JoshWilbur/Electronic-Speed-Controller/Schematics/H_Bridge_SchematicV3.pdf

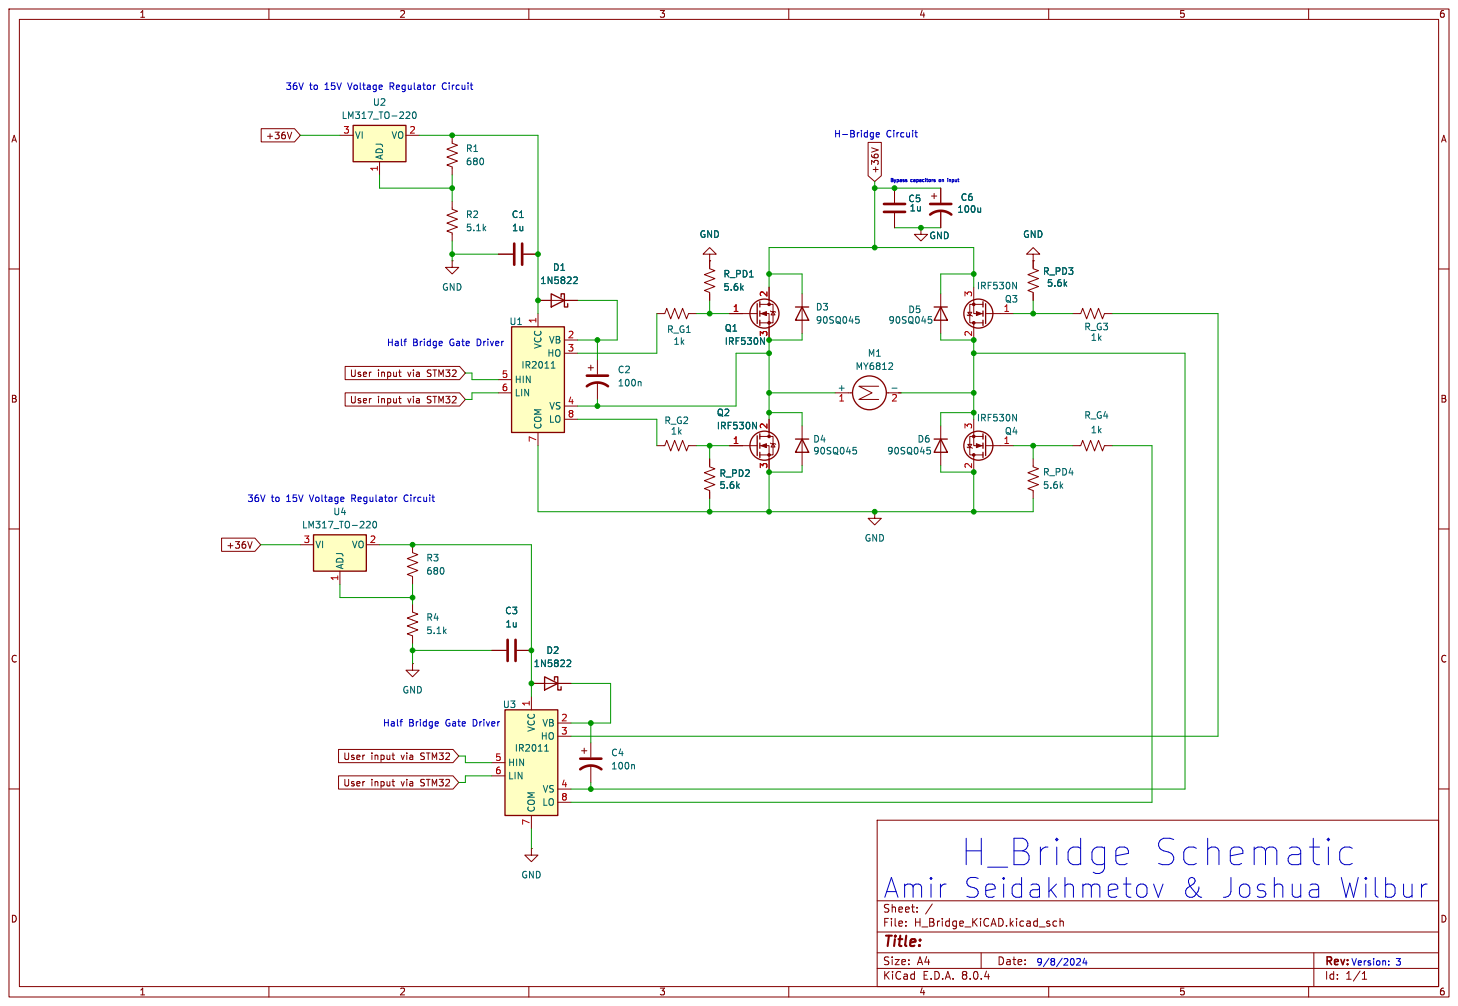
[picture p34: page 1]

Id: 1/1 Title: File: H_Bridge_KiCAD.kicad_sch Sheet: / VCC

1 VB 2 HO 3 VS 4 HIN 5

Half Bridge Gate Driver
