JoshWilbur/Electronic-Speed-Controller/Schematics/H_Bridge_SchematicV2.pdf

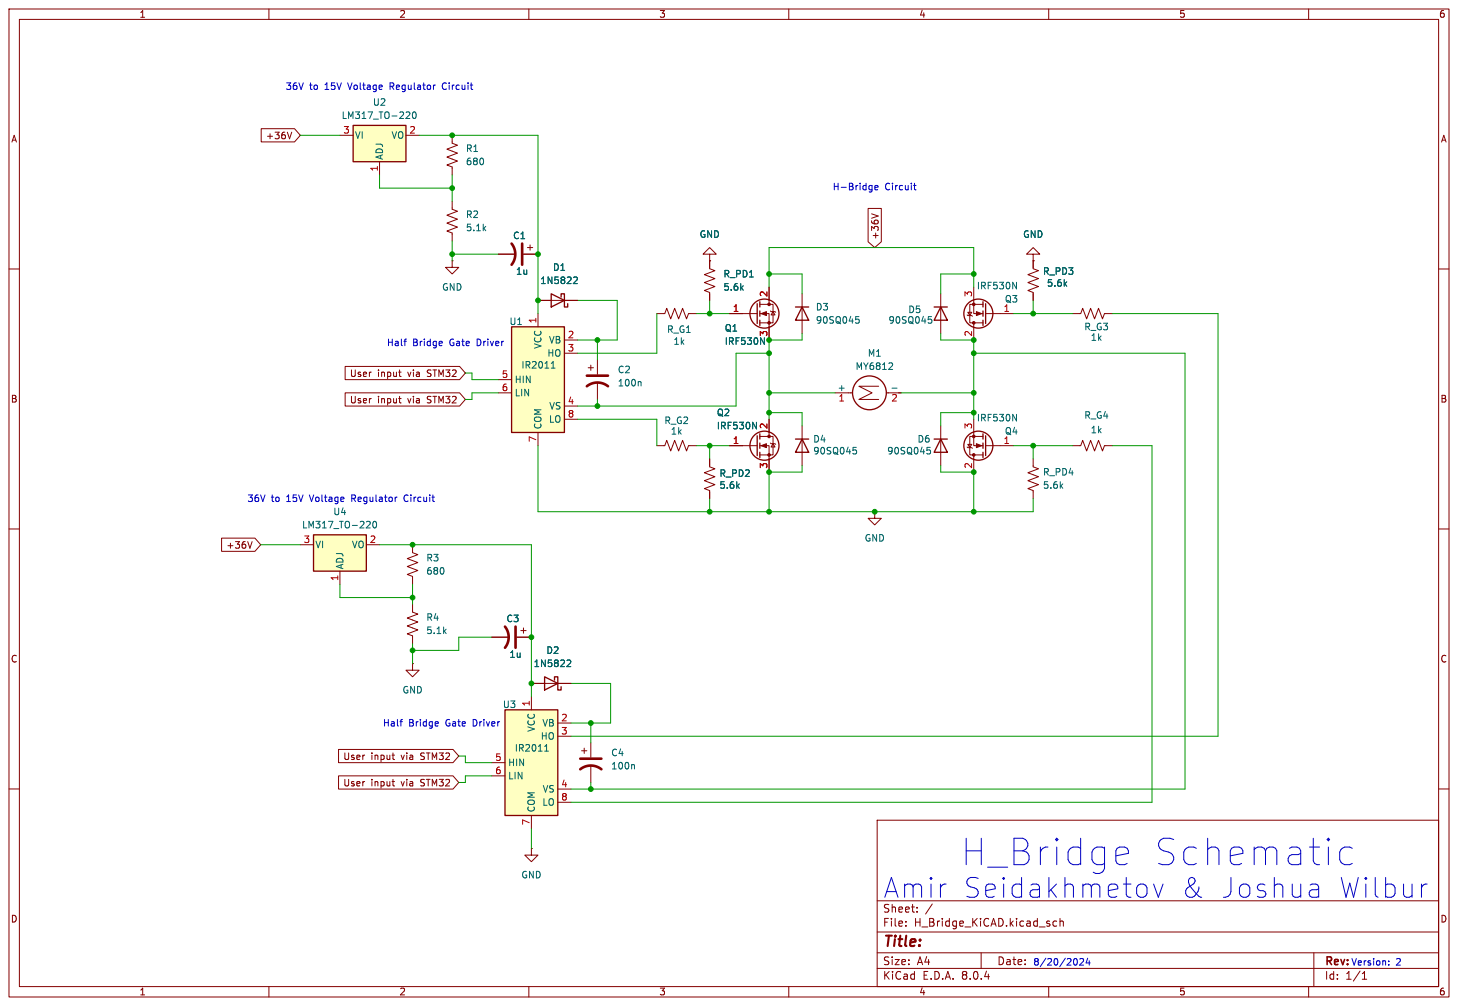
[picture p35: page 1]

1 VB 2 HO 3 VS 4 HIN 5

Id: 1/1 Title: File: H_Bridge_KiCAD.kicad_sch Sheet: /
