JoshWilbur/Electronic-Speed-Controller/Schematics/H_Bridge_SchematicV4.pdf

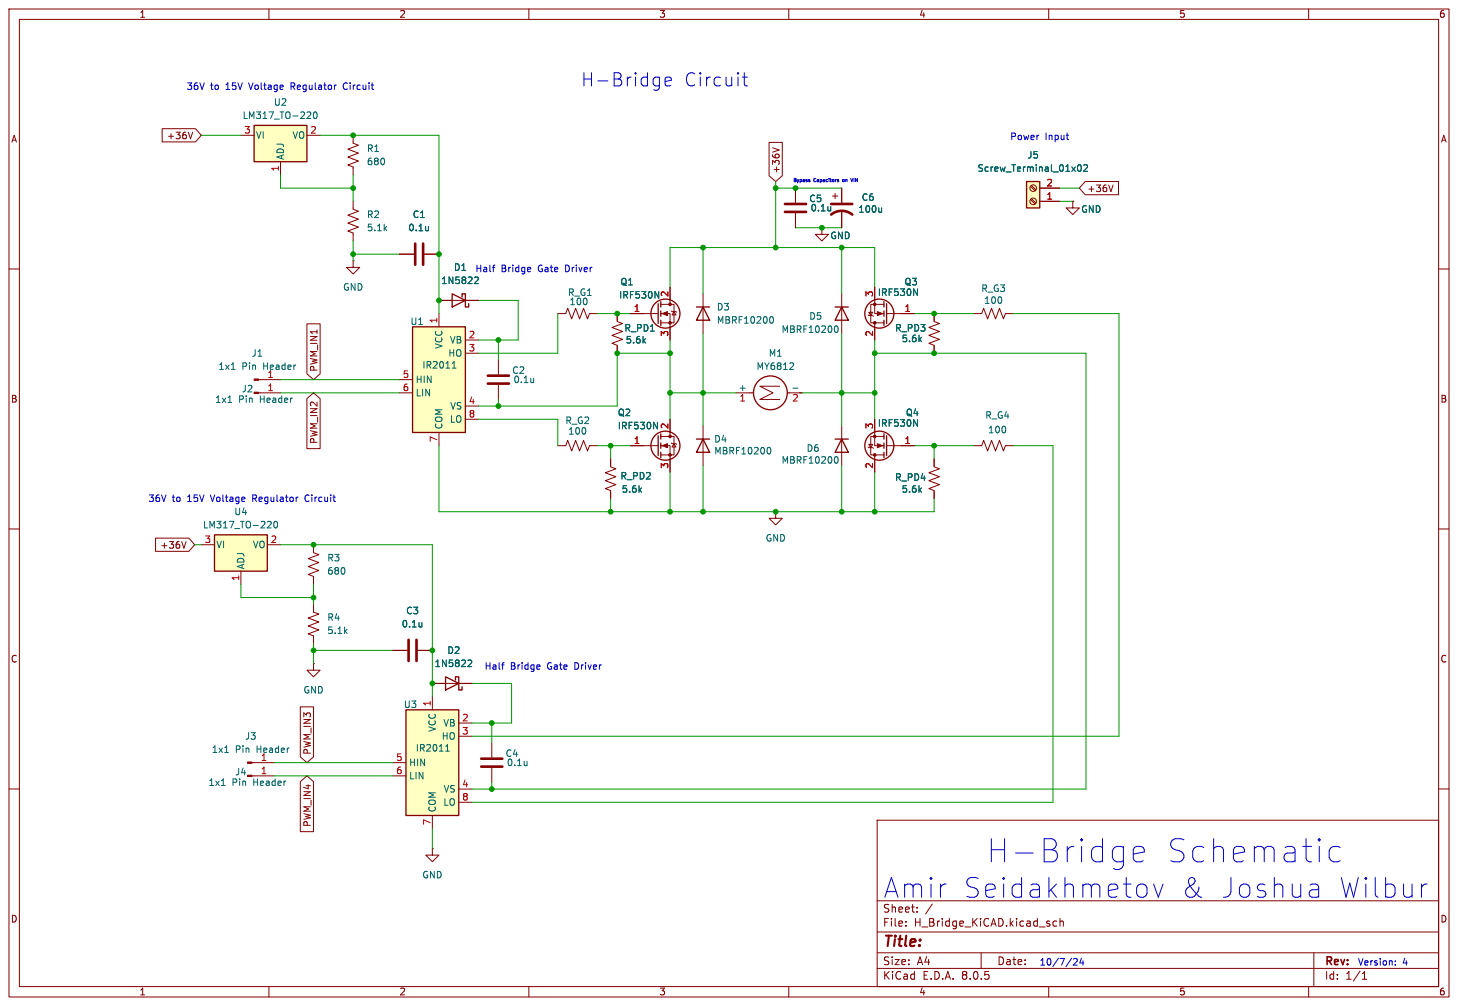
[picture p36: page 1]

1 VB 2 HO 3 VS 4 HIN 5
