JoshWilbur/Electronic-Speed-Controller/Core/Inc/user_input.h

// Header file for the user_input.c program
#ifndef INC_USER_INPUT_H_
#define INC_USER_INPUT_H_

// Function prototypes
int user_input();
int update_input(int current_val, int prior_val, int feedback);
int input_to_rpm(int u_input);
void HAL_GPIO_EXTI_Callback(uint16_t GPIO_Pin);

// Global variable for direction flag
extern volatile int dir_flag; // motor direction flag


#endif /* INC_USER_INPUT_H_ */
