JoshWilbur/Electronic-Speed-Controller/Core/Inc/adc_reader.h

/*
 * adc_reader.h
 *
 *  Created on: Nov 11, 2024
 *      Author: amirs
 */

#ifndef SRC_ADC_READER_H_
#define SRC_ADC_READER_H_



#endif /* SRC_ADC_READER_H_ */

#ifndef __ADC_READER_H
#define __ADC_READER_H

#include "stm32l4xx_hal.h"

extern uint32_t adc_value;       // Global ADC raw value
extern float v_bat;    // Global scaled battery voltage


uint32_t Read_ADC_Value(void);     // Prototype for reading ADC
float Scale_ADC_to_Voltage(uint32_t adc_value);  // Prototype for scaling to voltage

#endif /* __ADC_READER_H */
